hanneslinder/esp-pixel-matrix/esp32/src/websocket/WebSocketHandler.h

#pragma once

#include "../types/CommonTypes.h"
#include <Arduino.h>
#include <ArduinoJson.h>
#include <ESPAsyncWebServer.h>

// Forward declarations
class MatrixController;
class TextDisplayHandler;
class CustomDataHandler;
class QuietHoursHandler;

namespace WebSocketHandler {

// Initialize the WebSocket handler with required dependencies
void init(MatrixController* matrixCtrl, TextItem* textItems, AsyncWebSocket* websocket,
    char* socketBuffer, int* bufferIndex, const int bufferSize,
    TextDisplayHandler* textDisplayHandler, CustomDataHandler* customDataHandler,
    QuietHoursHandler* quietHoursHandler);

// Main WebSocket message handler
void handleMessage(void* arg, uint8_t* data, size_t len);

// Event handlers
void onConnect(AsyncWebSocketClient* client);
void onDisconnect(AsyncWebSocketClient* client);
void onError(AsyncWebSocketClient* client);

// Utility functions
void sendPixels();
void sendState();
void broadcastConfigUpdate(); // Notify all clients of config changes

} // namespace WebSocketHandler
